TutuThePerson/StudyKeyChain/Firmware/main/display.h

#pragma once

void display_init(void);
void display_refresh(void);
void display_show_idle(int sessions_today);
void display_show_session_length(int seconds);
void display_show_timer(int seconds);
void display_show_break(int seconds);
void display_show_session_complete(int sessions_today);
void display_show_hydration_reminder(void);
void display_show_low_battery(void);
void display_clear(void);
